Franzininho/Franzininho-WiFi/Franzininho-WIFI-kicad/imagens/Franzininho WIFI2.png

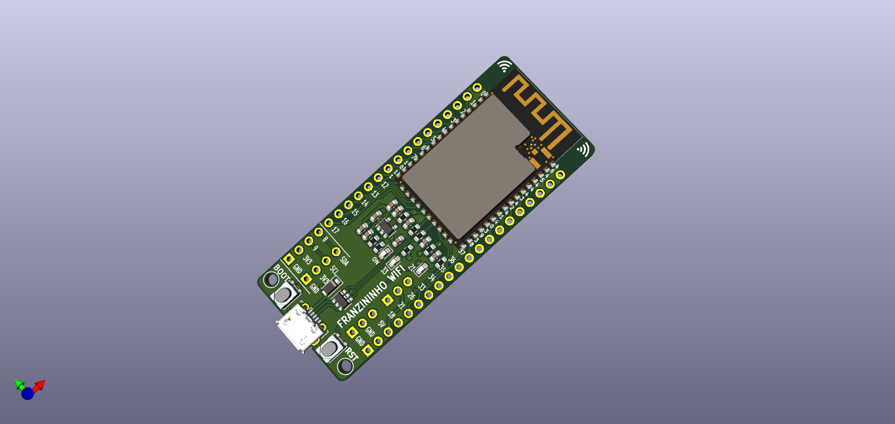
Franzininho-WIFI-kicad/imagens/Franzininho WIFI2.png
